malferov/robocup/docs/bot2.jpg

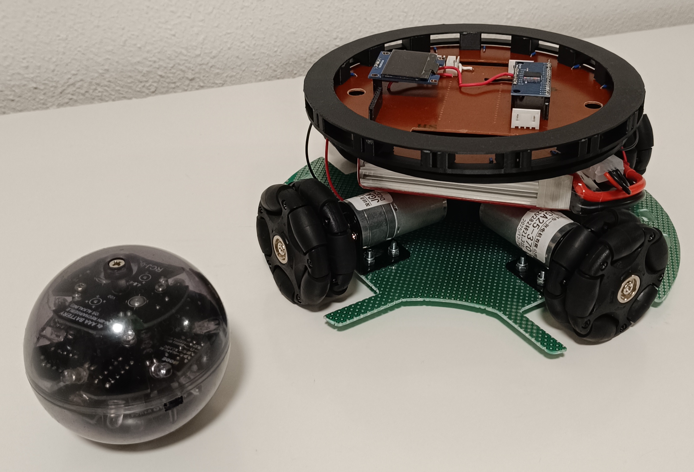
docs/bot2.jpg
