malferov/robocup/docs/motor.jpg

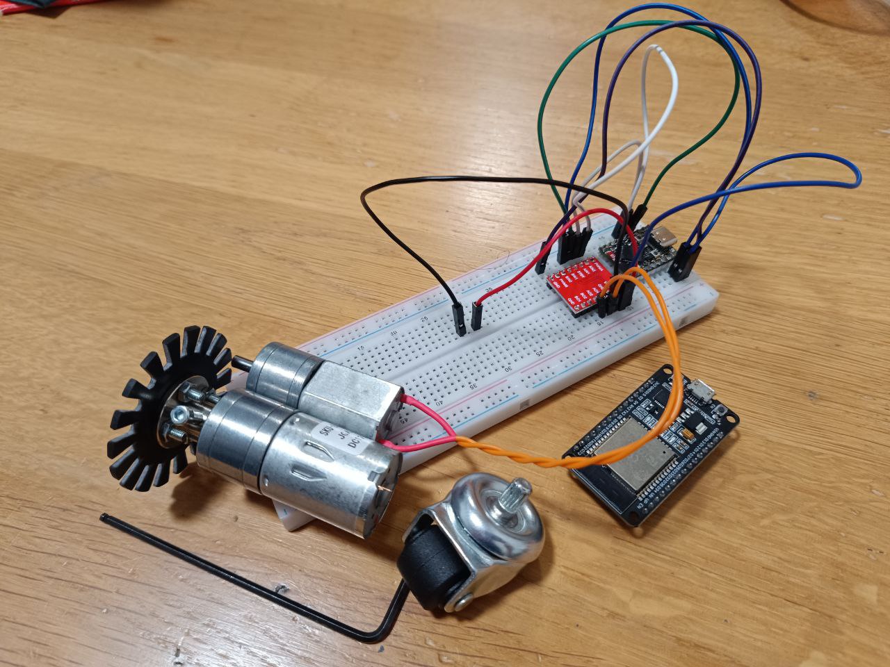
docs/motor.jpg
