malferov/robocup/pcb/mainboard/misc/pie15.png

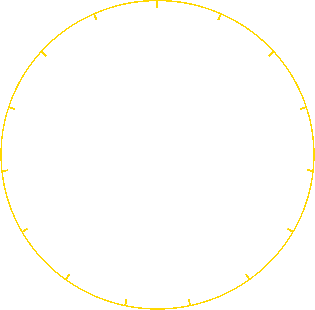
pcb/mainboard/misc/pie15.png
