malferov/robocup/docs/motor_size_test.jpg

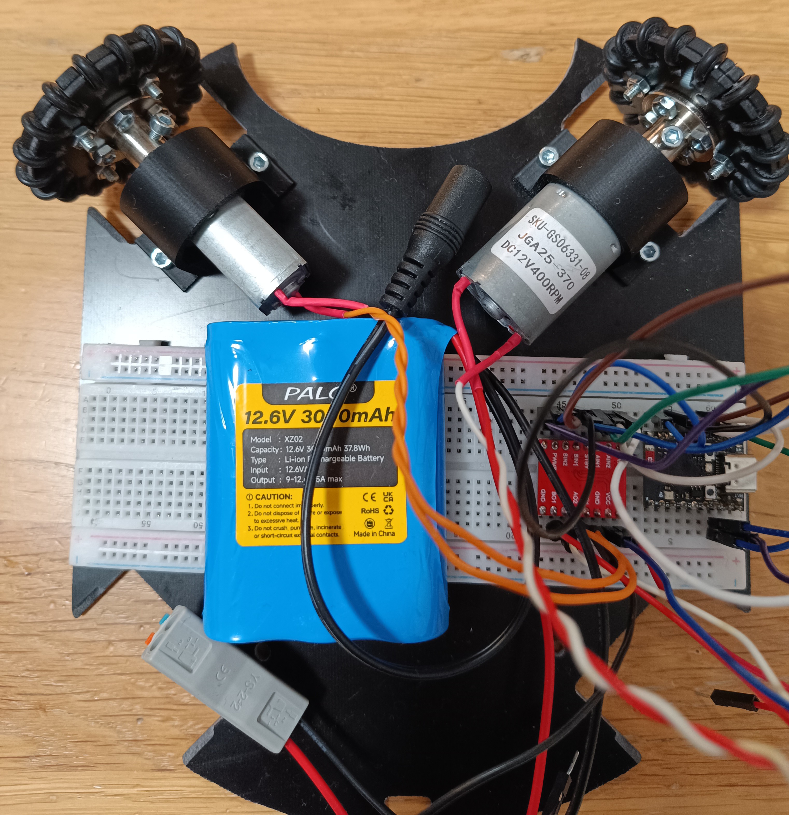
docs/motor_size_test.jpg
