malferov/robocup/code/base/base.ino

#include <Wire.h>
#include <Adafruit_GFX.h>
#include "DFRobot_BMM150.h"
#include <Preferences.h>
DFRobot_BMM150_I2C bmm150(&Wire1, 0x13);
Preferences prefs;

#define BOT_ID 1 // 1 or 2

#if BOT_ID == 1
#include <Adafruit_SSD1306.h>
#define MUX_SIG 26
#define MUX_S3 2
#define MUX_S2 4
#define MUX_S1 5
#define MUX_S0 18
#define MODE_BUTTON 19
#define START_BUTTON 23
#define INIT_DISTANCE 0
#define LINE_LEFT 34
#define LINE_CENTER 36
#define LINE_RIGHT 39
#else
#include <Adafruit_SH110X.h>
#define MUX_SIG 13
#define MUX_S3 15
#define MUX_S2 2
#define MUX_S1 0
#define MUX_S0 4
#define MODE_BUTTON 26
#define START_BUTTON 23
#define INIT_DISTANCE 200 // fixed distance for bot2
#define LINE_LEFT 32
#define LINE_CENTER 33
#define LINE_RIGHT 25
#endif

#define SCREEN_WIDTH 128
#define SCREEN_HEIGHT 64
#define CAM_WIDTH 160
#define CAM_WIDTH_FL 160.0

#define SDA_PIN 21
#define SCL_PIN 22

#define SERIAL_RX 3
#define SERIAL_TX 1
#define SERIAL2_RX 16
#define SERIAL2_TX 17

#define ANALOG_MAX 4095
#define SEGMENT_ANGLE 24

#define PRESS_DELAY 500   // ms
#define SHOOT_DELAY 500  // ms
#define CMD_DELAY 0
//sensitivety
#define MAG_SENSETIVITY 1

//deviation settings
#define ACPT_BALLDEVIATION 8 //acceptable ball deviation angle
#define ACPT_MAGDEVIATION 8 //acceptable magnetic deviation angle
#define ACPT_DISTANCE 75 // mm
#define ONE_SPEED 15
#define MAX_BALL_DEVIATION 8 //degrees
//fix for the Goal keeper mode
#define FIX_SPEED_LEFT 0 //<360
#define FIX_SPEED_RIGHT 0 //>0
//line config
#define LINE_THRESHOLD 4095

# if BOT_ID == 1
#define MIN_SPEED 7
#define WHITE SSD1306_WHITE
#define BLACK SSD1306_BLACK
Adafruit_SSD1306 display(SCREEN_WIDTH, SCREEN_HEIGHT, &Wire, -1);
#else
#define MIN_SPEED 15
#define WHITE SH110X_WHITE
#define BLACK SH110X_BLACK
Adafruit_SH1106G display(SCREEN_WIDTH, SCREEN_HEIGHT, &Wire, -1);
#endif

typedef struct {
  char dir;
  int deviation;
  int left;
  int right;
  int center;
  int centerDeviation; // L negative; R positive; 30 degrees range
} goalPositionT;

typedef struct {
  goalPositionT goalPosition;
  int distance;
} CAMT;

goalPositionT zeroPosition = goalPositionT('L',0,0,0,0);
CAMT cam = CAMT(zeroPosition, INIT_DISTANCE);
int ballHeading = 0;  // ahead by default
int ballDeviation = 0;
int accept_distance = ACPT_DISTANCE;
int angs[15];         // sensors angles

int left_line = 0;
int right_line = 0;

int MS[] = {0,0,0,0};

String Modes[] = {
  "CALIBRATION",
  "TEST",
  "LINE_ACTIVE"
};
int mode_len = 3;
int mode_num = 0;
bool idle = true;
String mode = Modes[mode_num];
int max_speed = MIN_SPEED + ONE_SPEED * 1; // 1, 2 or 3

unsigned long button_timer;
unsigned long move_timer;
unsigned long shoot_timer;
unsigned long distance_reset_timer;
bool need_reset = false;
char msg[50] = {0};

#define CALIBRATION_TIME 15000
float mag_x_offset = 0;
float mag_y_offset = 0;
int magHeading = 0;
int magChase = 0;
int magDeviation = 0;
bool line_active = true;
bool cam_active = true;

String getValue(String data, char separator, int index) {
  int found = 0;
  int strIndex[] = {0, -1};
  int maxIndex = data.length()-1;

  for(int i=0; i<=maxIndex && found<=index; i++){
    if(data.charAt(i)==separator || i==maxIndex){
        found++;
        strIndex[0] = strIndex[1]+1;
        strIndex[1] = (i == maxIndex) ? i+1 : i;
    }
  }
  return found>index ? data.substring(strIndex[0], strIndex[1]) : "";
}

void Target(int M1, int M2, int M3, int M4) {
  Serial.printf("target:%d:%d:%d:%d\n", M1,M2,M3,M4);
}

int getIR(int channel) {
  // select channel
  digitalWrite(MUX_S3, (channel >> 3) & 0x1);
  digitalWrite(MUX_S2, (channel >> 2) & 0x1);
  digitalWrite(MUX_S1, (channel >> 1) & 0x1);
  digitalWrite(MUX_S0, channel & 0x1);
  // read value
  int val = analogRead(MUX_SIG);
  // invert
  val = ANALOG_MAX - val;
  // normalization
  //val = (ANALOG_MAX - val) / ANALOG_MAX * 100;
  // noise
  // ANALOG_MAX * 0.01 = 40
  if (val >= 40) {
    return 1;
  }
  return 0;
}

void calcBallHeading() {

  int angle = ballHeading;
  int irs[15];
  int sum = 0;
  int cnt = 0;
  // get current angle
  // see ChatGPT Circular Mean (Vector Averaging) for trig solution
  // and Mean Delta lightweight option when all angles lie on the same "side" of the circle
  for (int i = 0; i < 15; i++) {
    irs[i] = getIR(i);
    if (irs[i] == 1) {
      cnt++;
      int delta = angs[i] - angle;
      if (delta > 180) {
        delta -= 360;
      }
      if (delta < -180) {
        delta += 360;
      }
      sum = sum + delta;
    }
  }
  if (cnt > 0) {
    // low-pass filter 10%
    angle += (sum / cnt) * 0.1;
  }
  // wrap to 0–360
  if (angle < 0) {
    angle += 360;
  }
  if (angle >= 360) {
    angle -= 360;
  }
  ballHeading = angle;
}

void getCAM() {
  String command = Serial2.readStringUntil('\n');
  if (command[0] == 'L' || command[0] == 'R') {
    //char dir = getValue(command,':',0)[0];
    //int deviation = getValue(command,':',1).toInt();
    int left = getValue(command,':',2).toInt();
    int right = getValue(command,':',3).toInt();
    int center = getValue(command,':',4).toInt();
    // calculate average 10/90
    center = 0.1 * center + 0.9 * cam.goalPosition.center;
    // recalc dir & dev
    char dir = 'L';
    if (center > CAM_WIDTH/2) dir = 'R';
    int deviation = 8 * abs(center - CAM_WIDTH/2) / (CAM_WIDTH/2);
    int centerDev = 30 * (center - CAM_WIDTH/2) / (CAM_WIDTH/2);
    // set position
    cam.goalPosition = goalPositionT(dir, deviation, left, right, center, centerDev);
    // set distance
    int distance = getValue(command,':',5).toInt();
    // filter spikes
    if (abs(distance - cam.distance) < 10) {
      // calculate average 10/90
      cam.distance = 0.1 * distance + 0.9 * cam.distance;
    } else {
      // reset timeout
      if (!need_reset) {
        need_reset = true;
        distance_reset_timer = millis() + 1000;
      }
      unsigned long current = millis();
      if (current > distance_reset_timer) {
        cam.distance = distance;
        need_reset = false;
      }
    }
  }
}

void refreshDisplay() {
  display.clearDisplay(); //clear display
  if (mode == "CALIBRATION") {
    display.setCursor(0, 20);
    display.printf("mag heading %3d", magHeading);
  } else if (mode == "TEST") {
    display.setCursor(0,10);
    display.print("magHeading:");
    display.setCursor(0,20);
    display.print(magDeviation*MAG_SENSETIVITY);
    display.setCursor(0,30);
    display.print("BallHeading:");
    display.setCursor(0,40);
    display.print(ballHeading);
    display.setCursor(0, 50);
    display.printf("distance %3d", cam.distance);
    for(int i = 1; i < 5; i++) {
      display.setCursor(70 , i*10);
      display.print(MS[i-1]);
    }
  } else if (mode == "LINE_ACTIVE") {
    display.setCursor(0,20);
    display.printf("Left line: %3d", left_line);
    display.setCursor(0,40);
    display.printf("Right line: %3d", right_line);
  }
  // display the current mode
  display.setCursor(0, 0);
  display.printf("%s", mode);
  if (idle) {
    display.setCursor(SCREEN_WIDTH-6*4, 0); // Size 1: 6x8 pixel area
    display.printf("%s", "IDLE");
  }
  display.display();
}

bool buttonPressed(int button) {
  bool pressed = false;
  unsigned long current = millis();
  // last press at least PRESS_DELAY ms ago
  if (current > button_timer) {
    int state = digitalRead(button);
    if (state == LOW) {
      pressed = true;
      button_timer = current + PRESS_DELAY;
    }
  }
  return pressed;
}

void changeMode(int m = -1) {
  if (m == -1) {
    mode_num += 1;
    if (mode_num == mode_len) {
      mode_num = 0;
    }
  } else {
    mode_num = m;
  }
  mode = Modes[mode_num];
}

void shoot(int speed){
  Target(speed,speed,speed,speed);
  Serial2.write("shoot\n");
  delay(200);
  Target(0,0,0,0);
  delay(200);
}

bool move_timeout(int speed, int duration) {
  unsigned long current_time = millis();
  // wait for previous command done
  if (current_time > move_timer) {
    // set new timer
    // rump up/down + duration + extra
    move_timer = current_time + speed * 2 + duration + CMD_DELAY;
    return true;
  }
  return false;
}

void getCompass() {

  sBmm150MagData_t magData = bmm150.getGeomagneticData();

  float x = magData.x - mag_x_offset;
  float y = magData.y - mag_y_offset;

  int heading = atan2(y, x) * 180.0 / PI;

  int delta = heading - magHeading;
  if (delta > 180) delta -= 360;
  if (delta < -180) delta += 360;

  // Smooth heading
  heading += delta * 0.1;

  // wrap to 0–360
  if (heading < 0) heading += 360;
  if (heading >= 360) heading -= 360;

  heading = 360 - heading;
  magHeading = heading;
}

void message(char m[]) {
  display.clearDisplay();
  display.setCursor(0, 20);
  display.print(m);
  display.display();
  delay(1000);
}

void autoCalibrate() {

  float x_min = 9999, x_max = -9999;
  float y_min = 9999, y_max = -9999;

  unsigned long startTime = millis();
  message("Rotate robot slowly..");
  int speed = ONE_SPEED * 1.1;

  if (move_timeout(speed, CALIBRATION_TIME)) {
    Serial.printf("speed4:%d:%d:%d:%d:%d\n", -speed, -speed, speed, speed, CALIBRATION_TIME);
  }

  while (millis() - startTime < CALIBRATION_TIME) {

    sBmm150MagData_t magData = bmm150.getGeomagneticData();

    float x = magData.x;
    float y = magData.y;

    if (x < x_min) x_min = x;
    if (x > x_max) x_max = x;
    if (y < y_min) y_min = y;
    if (y > y_max) y_max = y;

    delay(100);
  }

  mag_x_offset = (x_max + x_min) / 2.0;
  mag_y_offset = (y_max + y_min) / 2.0;
  message("Calibration complete");
}

void saveCalibration() {
  prefs.putFloat("x_off", mag_x_offset);
  prefs.putFloat("y_off", mag_y_offset);
  prefs.putBool("calibrated", true);
  message("Calibration saved");
}

void getLine() {
  right_line = analogRead(LINE_RIGHT);
  left_line = analogRead(LINE_LEFT);
}

void MSadd(int M1,int M2,int M3,int M4) {
  MS[0] += M1;
  MS[1] += M2;
  MS[2] += M3;
  MS[3] += M4;
}

void BetterTurnToMagnet() {
  int deviation = magDeviation * MAG_SENSETIVITY;
  MSadd(-deviation,-deviation,deviation,deviation);
}

void GoToBall(int speed){
  if (speed > 100) {
    speed = 100;
  }
  MSadd(-speed,-speed,-speed,-speed);
}

void setup() {

  Wire.begin(SDA_PIN, SCL_PIN);

  #if BOT_ID == 1
    display.begin(SSD1306_SWITCHCAPVCC, 0x3C);
  #else
    display.begin(0x3C);
  #endif

  // Size 1: 6x8 pixel area
  // Size 2: 12x16 pixels
  // display.setTextSize(2);
  display.setRotation(2);
  display.setTextColor(WHITE, BLACK);
  sprintf(msg, "CoreX bot%d", BOT_ID);
  message(msg);

  Serial.begin(9600, SERIAL_8N1, SERIAL_RX, SERIAL_TX);
  Serial.println();
  Serial2.begin(9600, SERIAL_8N1, SERIAL2_RX, SERIAL2_TX);
  Serial2.println();

  pinMode(MUX_S3, OUTPUT);  // set MUX_Sx as output
  pinMode(MUX_S2, OUTPUT);
  pinMode(MUX_S1, OUTPUT);
  pinMode(MUX_S0, OUTPUT);

  pinMode(MODE_BUTTON, INPUT_PULLUP);  // buttons
  pinMode(START_BUTTON, INPUT_PULLUP);

  // zero sensor angle
  angs[0] = 90 + SEGMENT_ANGLE/2;
  // sensors angles
  for (int i = 1; i < 15; i++) {
    angs[i] = angs[i-1] + SEGMENT_ANGLE;
    if (angs[i] >= 360) {
      angs[i] = angs[i] - 360;
    }
  }
  // init cam request
  Serial2.write("get_pos\n");

  // compass
  #if BOT_ID == 1
  #define W2_SDA 27
  #else
  #define W2_SDA 12
  #endif
  #define W2_SCL 14

  Wire1.begin(W2_SDA, W2_SCL);
  if (bmm150.begin() != BMM150_OK) {
    message("BMM150 init failed!");
  }

  bmm150.setOperationMode(BMM150_POWERMODE_NORMAL);
  bmm150.setPresetMode(BMM150_PRESETMODE_HIGHACCURACY);
  bmm150.setMeasurementXYZ(MEASUREMENT_X_ENABLE, MEASUREMENT_Y_ENABLE, MEASUREMENT_Z_DISABLE);

  prefs.begin("compass", false);

  if (prefs.getBool("calibrated", false)) {
    // Load stored offsets
    mag_x_offset = prefs.getFloat("x_off", 0);
    mag_y_offset = prefs.getFloat("y_off", 0);
    /*message("Calibration loaded");
    sprintf(msg, "x offset: %.2f", mag_x_offset);
    message(msg);
    sprintf(msg, "y offset: %.2f", mag_y_offset);
    message(msg);*/
  } else {
    message("No calibration found.");
    message("Auto calibration...");
    autoCalibrate();
    saveCalibration();
  }
}

void loop() {

  if (Serial2.available()) {
    getCAM();
    Serial2.write("get_pos\n");
  }

  calcBallHeading();
  ballDeviation = ballHeading;
  if (ballDeviation > 180) ballDeviation -= 360;
  getCompass();
  magDeviation = magChase - magHeading;
  if (magDeviation > 180) magDeviation -= 360;
  if (magDeviation < -180) magDeviation += 360;
  getLine();

  if (buttonPressed(MODE_BUTTON)) {
    if (idle) changeMode();
  }
  if (buttonPressed(START_BUTTON)) {
    if (idle) {
      idle = false;
      changeMode(mode_num); // run selected mode
      if (mode == "BALL_CHASE" || mode == "MAG_SEARCH" || mode == "TEST") magChase = magHeading;
      else if (mode == "SPEED_1" || mode == "SPEED_2" || mode == "SPEED_3") {
        int selected_speed = mode_num-(mode_len-4); // 1, 2 or 3
        max_speed = MIN_SPEED + ONE_SPEED * selected_speed;
        sprintf(msg, "Speed %d selected", selected_speed);
        message(msg);
        idle = true;
      } else if (mode == "LINE_ACTIVE") {
        if (line_active) {
          line_active = false;
          message("Line off");
        } else {
          line_active = true;
          message("Line on");
        }
        idle = true;
      } else if (mode == "CAM_ACTIVE") {
        if (cam_active) {
          cam_active = false;
          message("CAM off");
        } else {
          cam_active = true;
          message("CAM on");
        }
        idle = true;
      }
    } else {
      idle = true; // off
      if (mode == "TEST") {
          Target(0,0,0,0);
      }
    }
  }

  refreshDisplay();

  // actions
  if (!idle) {

    // lines
    if (line_active) {
      if (right_line == LINE_THRESHOLD && left_line == LINE_THRESHOLD) {
        // shift ahead
        Target(50,50,50,50);
        delay(50);
        if (right_line == LINE_THRESHOLD && left_line == LINE_THRESHOLD) {
          // still white -> reverse
          Target(-50,-50,-50,-50);
          delay(400);
          Target(0,0,0,0);
        } else {
          // left own white goal area -> forward
          Target(50,50,50,50);
          delay(400);
          Target(0,0,0,0);
        }
      } else if (right_line == LINE_THRESHOLD) {
        // jog left
        Target(50,-50,50,-50);
        delay(200);
        Target(0,0,0,0);
      } else if (left_line == LINE_THRESHOLD) {
        // jog right
        Target(-50,50,-50,50);
        delay(200);
        Target(0,0,0,0);
      }
    }

    if (mode == "CALIBRATION") {
      message("Auto calibration...");
      autoCalibrate();
      saveCalibration();
      idle = true;
    } else if (mode == "TEST") {
      //set everything to 0
      for (int i = 0; i < 4; i++) {
        MS[i] = 0;
      }
      int speed = abs(ballDeviation) * 1;//0.8;
      int acceleration = 75;
      if (speed > 255) {
        speed = 255;
      }
      BetterTurnToMagnet();
      if (ballHeading > 80 && ballHeading < 280) {
        GoToBall(speed);
      } else {
        if (ballHeading > 20 && ballHeading < 340) {
          if (ballHeading >= 0 && ballHeading < 180) {
            MSadd(-speed,speed,-speed,speed);
          } else if (ballHeading >= 180 && ballHeading < 360) {
            MSadd(speed,-speed,speed,-speed);
          }
        } else {
          // positioned at ball
          if (cam.distance > 50) {
            MSadd(acceleration,acceleration,acceleration,acceleration);
          } else {
            shoot(150);
          }
        }
      }
      Target(MS[0],MS[1],MS[2],MS[3]);
    }
  }
  // cycle end
  delay(1);
}
