malferov/robocup/code/cam/cam_init.cpp

#include "Arduino.h"
#include "esp_camera.h"
//#include <WiFi.h>

// ===========================
// Select camera model in board_config.h
// ===========================
#include "board_config.h"

// ===========================
// Enter your WiFi credentials
// ===========================
/*
const char *ssid = "";
const char *password = "";
void startCameraServer();
*/

void camSetup() {

  camera_config_t config;
  // PWR
  config.pin_pwdn = PWDN_GPIO_NUM;
  config.pin_reset = RESET_GPIO_NUM;
  // Control pins
  config.pin_xclk = XCLK_GPIO_NUM;
  config.pin_pclk = PCLK_GPIO_NUM;
  config.pin_vsync = VSYNC_GPIO_NUM;
  config.pin_href = HREF_GPIO_NUM;
  // SCCB
  config.pin_sccb_sda = SIOD_GPIO_NUM;
  config.pin_sccb_scl = SIOC_GPIO_NUM;
  // LED
  config.ledc_channel = LEDC_CHANNEL_0;
  config.ledc_timer = LEDC_TIMER_0;
  // Data
  config.pin_d0 = Y2_GPIO_NUM;
  config.pin_d1 = Y3_GPIO_NUM;
  config.pin_d2 = Y4_GPIO_NUM;
  config.pin_d3 = Y5_GPIO_NUM;
  config.pin_d4 = Y6_GPIO_NUM;
  config.pin_d5 = Y7_GPIO_NUM;
  config.pin_d6 = Y8_GPIO_NUM;
  config.pin_d7 = Y9_GPIO_NUM;
  //
  config.xclk_freq_hz = 20000000;
  //config.frame_size = FRAMESIZE_96X96;
  config.frame_size = FRAMESIZE_QQVGA; // (160x120)
  config.pixel_format = PIXFORMAT_RGB565;
  config.grab_mode = CAMERA_GRAB_WHEN_EMPTY;
  config.fb_location = CAMERA_FB_IN_PSRAM;
  //config.fb_location = CAMERA_FB_IN_DRAM;
  config.fb_count = 1; //2;

  // camera init
  esp_err_t err = esp_camera_init(&config);
  if (err != ESP_OK) {
    Serial.printf("Camera init failed with error 0x%x", err);
    return;
  }

  sensor_t *s = esp_camera_sensor_get();

  s->set_whitebal(s, 0);      // disable auto white balance
  s->set_awb_gain(s, 0);
  s->set_gain_ctrl(s, 0);
  s->set_exposure_ctrl(s, 0); // disable auto exposure

  s->set_brightness(s, 0);
  s->set_saturation(s, 1);
  s->set_contrast(s, 1);

  //s->set_agc_gain(s, 16); // bright at sunlight
  s->set_agc_gain(s, 8);
  //s->set_agc_gain(s, 4);  // dark

  //s->set_aec_value(s, 300);
  //s->set_aec_value(s, 180); // bright at sunlight
  s->set_aec_value(s, 120);
  //s->set_aec_value(s, 80); // dark

/*
  WiFi.begin(ssid, password);
  WiFi.setSleep(false);

  Serial.print("WiFi connecting");
  while (WiFi.status() != WL_CONNECTED) {
    delay(500);
    Serial.print(".");
  }
  Serial.println("");
  Serial.println("WiFi connected");

  startCameraServer();
  Serial.println("Camera Ready");
  Serial.print(WiFi.localIP());
  Serial.println("' to connect");
*/
}
